Cosmo-Robot/Cosmo-Robot-Working/Codes/FINAL-CODE/level management/LEVEL3.cpp

#include "levelManage.h"
// /////////////////////////////////RAMP///////////////////////////////////////////////////////////////////////////////////////////////

// /////////////////////////////////Definitions///////////////////////////////////////////////////////////////////////////////////////////////
void level3(){
    lineFollow(); //go though the ramp
}
